beattie/stm32f723-USB-demo/src/main.rs

#![no_std]
#![no_main]

use embassy_executor::Spawner;
use embassy_stm32::gpio::{Level, Output, Speed};
use embassy_time::Timer;
use panic_halt as _;

#[embassy_executor::main]
async fn main(_spawner: Spawner) {
    let p = embassy_stm32::init(Default::default());

    // TODO: add peripherals here

    let mut led = Output::new(p.PA5, Level::Low, Speed::Low);

    loop {
        led.set_high();
        Timer::after_millis(500).await;
        led.set_low();
        Timer::after_millis(500).await;
    }
}
