beattie/stm32f723-USB-demo/interposer/build.rs

use std::{env, fs, path::PathBuf};

fn main() {
    let out = PathBuf::from(env::var("OUT_DIR").unwrap());
    fs::copy("memory.x", out.join("memory.x")).unwrap();
    println!("cargo:rustc-link-search={}", out.display());
    println!("cargo:rerun-if-changed=memory.x");
    println!("cargo:rerun-if-changed=build.rs");
}
